Nieko27/Frame-Workshop/KICAD Projects/_Shared/Models/WLCSP-4(0.8x0.8).step

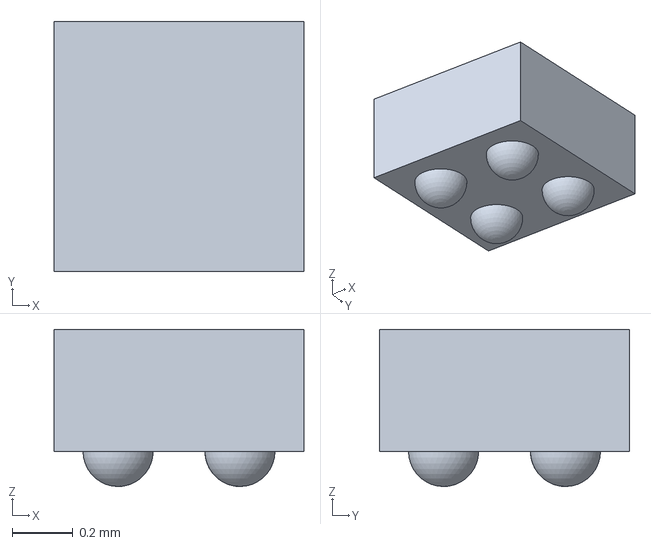
[picture p35: CAD file, 2026-09-01]
KICAD Projects/_Shared/Models/WLCSP-4(0.8x0.8).step
0.82 x 0.82 x 0.515 mm
