Nieko27/Frame-Workshop/3D Models/Versipellis/VeriEV1.stl

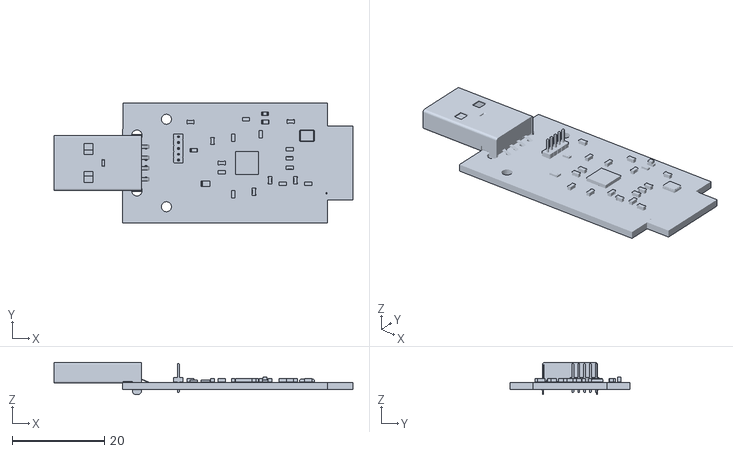
[picture p36: CAD file, 2026-05-19]
3D Models/Versipellis/VeriEV1.stl
64.9 x 26.0 x 7.00
