Nieko27/Frame-Workshop/KICAD Projects/_Shared/Models/USB Connector Type A male, SMT.STEP

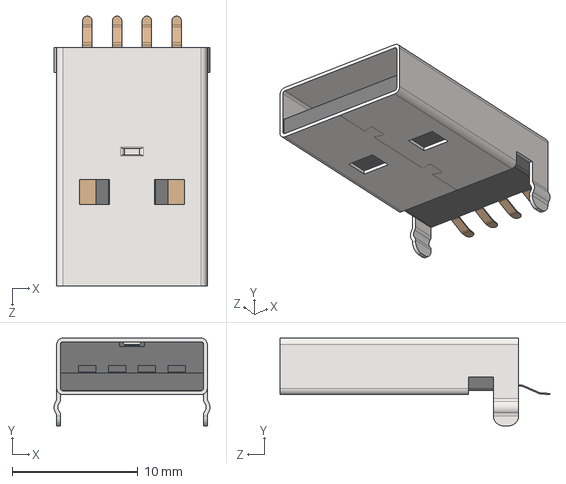
[picture p37: CAD file, 2026-05-13]
KICAD Projects/_Shared/Models/USB Connector Type A male, SMT.STEP
12.4 x 7.00 x 21.5 mm
