Nieko27/Frame-Workshop/KICAD Projects/_Shared/Models/USB-05.stp

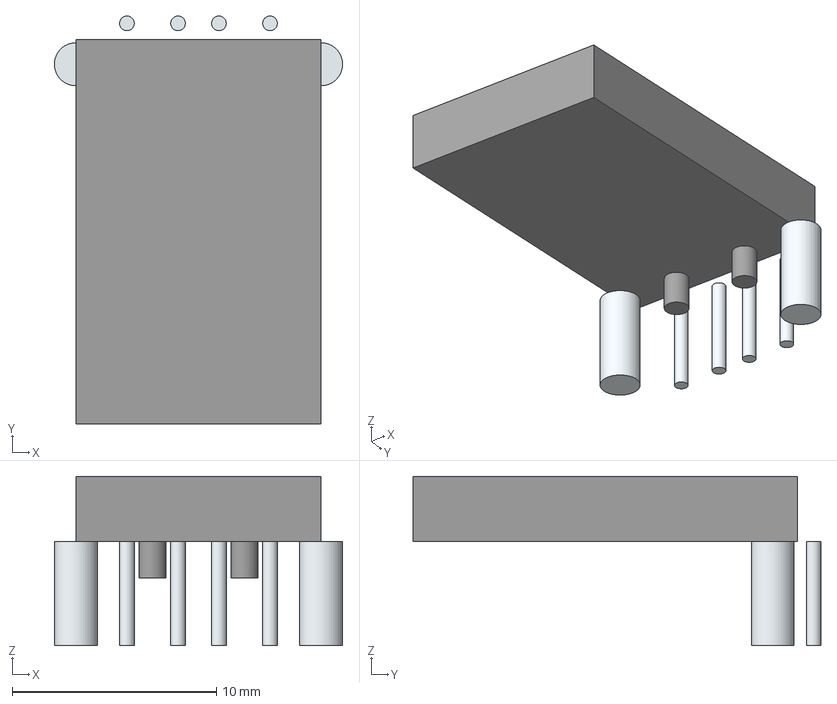
[picture p38: CAD file, 2026-05-02]
KICAD Projects/_Shared/Models/USB-05.stp
14.1 x 20.0 x 8.27 mm
Lugs x 8
Leads x 8
